sparkfun/SparkFun_USB-C_Host_Shield/docs/assets/img/hardware/shield_pins_marked.jpg

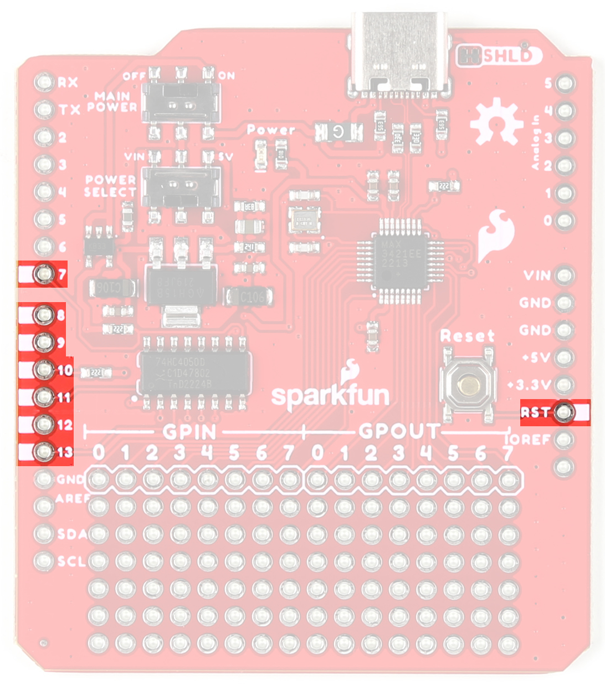
docs/assets/img/hardware/shield_pins_marked.jpg
