sparkfun/SparkFun_USB-C_Host_Shield/docs/assets/img/software/port2.png

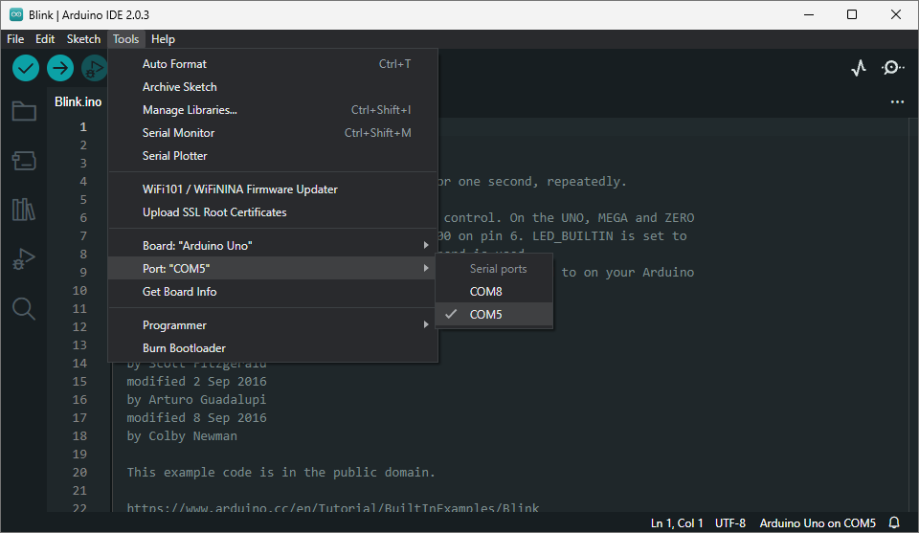
docs/assets/img/software/port2.png
