sparkfun/SparkFun_USB-C_Host_Shield/docs/assets/img/software/port.png

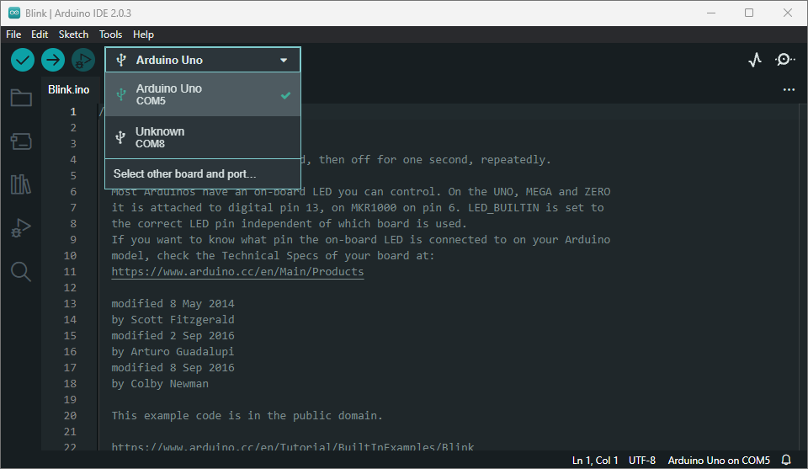
docs/assets/img/software/port.png
